Tinkerforge/gps-v2-bricklet/software/src/firefly_x1.c

/* gps-v2-bricklet
 * Copyright (C) 2016 Olaf Lüke <olaf@tinkerforge.com>
 * Copyright (C) 2020 Matthias Bolte <matthias@tinkerforge.com>
 *
 * firefly_x1.c: SPI communication with FireFly X1 GPS module
 *
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
 * You should have received a copy of the GNU Lesser General Public
 * License along with this library; if not, write to the
 * Free Software Foundation, Inc., 59 Temple Place - Suite 330,
 * Boston, MA 02111-1307, USA.
 */

#include "firefly_x1.h"

#include "xmc_spi.h"
#include "xmc_gpio.h"

#include "bricklib2/utility/ringbuffer.h"
#include "bricklib2/utility/led_flicker.h"
#include "bricklib2/protocols/tfp/tfp.h"
#include "bricklib2/hal/system_timer/system_timer.h"
#include "bricklib2/bootloader/bootloader.h"
#include "configs/config_firefly_x1.h"

#include "minmea.h"
#include "communication.h"

extern FireFlyX1 firefly_x1;

#define firefly_x1_rx_irq_handler IRQ_Hdlr_11
#define firefly_x1_tx_irq_handler IRQ_Hdlr_12

void __attribute__((optimize("-O3"))) firefly_x1_rx_irq_handler(void) {
	while(!XMC_USIC_CH_RXFIFO_IsEmpty(FIREFLY_X1_USIC)) {
		firefly_x1.ringbuffer_recv.buffer[firefly_x1.ringbuffer_recv.end] = FIREFLY_X1_USIC->OUTR;
		firefly_x1.ringbuffer_recv.end = (firefly_x1.ringbuffer_recv.end + 1) & FIREFLY_X1_RECV_BUFFER_MASK;

		firefly_x1.buffer_recv_counter++;
	}
}

void __attribute__((optimize("-O3"))) firefly_x1_tx_irq_handler(void) {
	while(!XMC_USIC_CH_TXFIFO_IsFull(FIREFLY_X1_USIC)) {
		FIREFLY_X1_USIC->IN[0] = firefly_x1.buffer_send[firefly_x1.buffer_send_index];
		firefly_x1.buffer_send_index++;
		if(firefly_x1.buffer_send_index == FIREFLY_X1_SEND_BUFFER_SIZE) {
			XMC_USIC_CH_TXFIFO_DisableEvent(FIREFLY_X1_USIC, XMC_USIC_CH_TXFIFO_EVENT_CONF_STANDARD);
			return;
		}
	}
}

void firefly_x1_init(FireFlyX1 *firefly_x1) {
	// Initialize the whole struct as zero
	memset(firefly_x1, 0, sizeof(FireFlyX1));
	firefly_x1->buffer_send_index = 0;
	firefly_x1->state = FIREFLY_X1_STATE_WAIT_FOR_INTERRUPT;
	firefly_x1->wait_8ms_start_time = 0;
	firefly_x1->fix_led_state.config = LED_FLICKER_CONFIG_EXTERNAL;
	firefly_x1->fix_led_config = GPS_V2_FIX_LED_CONFIG_SHOW_FIX;
	ringbuffer_init(&firefly_x1->ringbuffer_recv, FIREFLY_X1_RECV_BUFFER_SIZE, (uint8_t*)firefly_x1->buffer_recv);

	// USIC channel configuration
	const XMC_SPI_CH_CONFIG_t channel_config = {
		.baudrate       = 100000,
		.bus_mode       = XMC_SPI_CH_BUS_MODE_MASTER,
		.selo_inversion = XMC_SPI_CH_SLAVE_SEL_INV_TO_MSLS,
		.parity_mode    = XMC_USIC_CH_PARITY_MODE_NONE
	};

	// MISO pin configuration
	const XMC_GPIO_CONFIG_t mosi_pin_config = {
		.mode             = FIREFLY_X1_MOSI_PIN_AF,
		.output_level     = XMC_GPIO_OUTPUT_LEVEL_HIGH
	};

	// MOSI pin configuration
	const XMC_GPIO_CONFIG_t miso_pin_config = {
		.mode             = XMC_GPIO_MODE_INPUT_TRISTATE,
		.input_hysteresis = XMC_GPIO_INPUT_HYSTERESIS_STANDARD
	};

	// SCLK pin configuration
	const XMC_GPIO_CONFIG_t sclk_pin_config = {
		.mode             = FIREFLY_X1_SCLK_PIN_AF,
		.output_level     = XMC_GPIO_OUTPUT_LEVEL_HIGH
	};

	// SELECT pin configuration
	const XMC_GPIO_CONFIG_t select_pin_config = {
		.mode             = FIREFLY_X1_SELECT_PIN_AF,
		.output_level     = XMC_GPIO_OUTPUT_LEVEL_HIGH
	};

	// Interrupt pin configuration
	const XMC_GPIO_CONFIG_t interrupt_pin_config = {
		.mode             = XMC_GPIO_MODE_INPUT_TRISTATE,
		.output_level     = XMC_GPIO_OUTPUT_LEVEL_HIGH,
		.input_hysteresis = XMC_GPIO_INPUT_HYSTERESIS_STANDARD
	};

	// Reset pin configuration
	const XMC_GPIO_CONFIG_t nreset_pin_config = {
		.mode             = XMC_GPIO_MODE_OUTPUT_PUSH_PULL,
		.output_level     = XMC_GPIO_OUTPUT_LEVEL_HIGH, // not reset
	};

	// PPS pin configuration
	const XMC_GPIO_CONFIG_t pps_pin_config = {
		.mode             = XMC_GPIO_MODE_INPUT_TRISTATE,
		.output_level     = XMC_GPIO_OUTPUT_LEVEL_HIGH,
		.input_hysteresis = XMC_GPIO_INPUT_HYSTERESIS_STANDARD
	};

	// LED pin configuration
	XMC_GPIO_CONFIG_t led_pin_config = {
		.mode             = XMC_GPIO_MODE_OUTPUT_PUSH_PULL,
		.output_level     = XMC_GPIO_OUTPUT_LEVEL_LOW
	};

	// Configure GPIO pins
	XMC_GPIO_Init(FIREFLY_X1_INTERRUPT_PIN, &interrupt_pin_config);
	XMC_GPIO_Init(FIREFLY_X1_NRESET_PIN, &nreset_pin_config);
	XMC_GPIO_Init(FIREFLY_X1_PPS_PIN, &pps_pin_config);
	XMC_GPIO_Init(FIREFLY_X1_FIX_LED_PIN, &led_pin_config);

	// Configure MISO pin
	XMC_GPIO_Init(FIREFLY_X1_MOSI_PIN, &miso_pin_config);

	// Initialize USIC channel in SPI master mode
	XMC_SPI_CH_Init(FIREFLY_X1_USIC, &channel_config);
	FIREFLY_X1_USIC->SCTR &= ~USIC_CH_SCTR_PDL_Msk; // Set passive data level to 0

	XMC_SPI_CH_SetBitOrderMsbFirst(FIREFLY_X1_USIC);

	XMC_SPI_CH_SetWordLength(FIREFLY_X1_USIC, (uint8_t)8U);
	XMC_SPI_CH_SetFrameLength(FIREFLY_X1_USIC, (uint8_t)64U);

	XMC_SPI_CH_SetTransmitMode(FIREFLY_X1_USIC, XMC_SPI_CH_MODE_STANDARD);

	// Configure the clock polarity and clock delay
	XMC_SPI_CH_ConfigureShiftClockOutput(FIREFLY_X1_USIC,
									     XMC_SPI_CH_BRG_SHIFT_CLOCK_PASSIVE_LEVEL_1_DELAY_DISABLED,
									     XMC_SPI_CH_BRG_SHIFT_CLOCK_OUTPUT_SCLK);
	// Configure Leading/Trailing delay
	XMC_SPI_CH_SetSlaveSelectDelay(FIREFLY_X1_USIC, 2);

	// Set input source path
	XMC_SPI_CH_SetInputSource(FIREFLY_X1_USIC, FIREFLY_X1_MISO_INPUT, FIREFLY_X1_MISO_SOURCE);

	// SPI Mode: CPOL=1 and CPHA=1
	FIREFLY_X1_USIC_CHANNEL->DX1CR |= USIC_CH_DX1CR_DPOL_Msk;

	// Configure transmit FIFO
	XMC_USIC_CH_TXFIFO_Configure(FIREFLY_X1_USIC, 48, XMC_USIC_CH_FIFO_SIZE_16WORDS, 8);

	// Configure receive FIFO
	XMC_USIC_CH_RXFIFO_Configure(FIREFLY_X1_USIC, 32, XMC_USIC_CH_FIFO_SIZE_16WORDS, 0);
//	FIREFLY_X1_USIC->RBCTR |= USIC_CH_RBCTR_SRBTM_Msk; // RX Interrupt for >= 0

	// Set service request for tx FIFO transmit interrupt
	XMC_USIC_CH_TXFIFO_SetInterruptNodePointer(FIREFLY_X1_USIC, XMC_USIC_CH_TXFIFO_INTERRUPT_NODE_POINTER_STANDARD, FIREFLY_X1_SERVICE_REQUEST_TX);  // IRQ FIREFLY_X1_IRQ_TX

	// Set service request for rx FIFO receive interrupt
	XMC_USIC_CH_RXFIFO_SetInterruptNodePointer(FIREFLY_X1_USIC, XMC_USIC_CH_RXFIFO_INTERRUPT_NODE_POINTER_STANDARD, FIREFLY_X1_SERVICE_REQUEST_RX);  // IRQ FIREFLY_X1_IRQ_RX
	XMC_USIC_CH_RXFIFO_SetInterruptNodePointer(FIREFLY_X1_USIC, XMC_USIC_CH_RXFIFO_INTERRUPT_NODE_POINTER_ALTERNATE, FIREFLY_X1_SERVICE_REQUEST_RX); // IRQ FIREFLY_X1_IRQ_RX

	// Set priority and enable NVIC node for transmit interrupt
	NVIC_SetPriority((IRQn_Type)FIREFLY_X1_IRQ_TX, FIREFLY_X1_IRQ_TX_PRIORITY);
	NVIC_EnableIRQ((IRQn_Type)FIREFLY_X1_IRQ_TX);

	// Set priority and enable NVIC node for receive interrupt
	NVIC_SetPriority((IRQn_Type)FIREFLY_X1_IRQ_RX, FIREFLY_X1_IRQ_RX_PRIORITY);
	NVIC_EnableIRQ((IRQn_Type)FIREFLY_X1_IRQ_RX);

	// Start SPI
	XMC_SPI_CH_Start(FIREFLY_X1_USIC);

	// Configure SCLK pin
	XMC_GPIO_Init(FIREFLY_X1_SCLK_PIN, &sclk_pin_config);

	// Configure slave select pin
	XMC_GPIO_Init(FIREFLY_X1_SELECT_PIN, &select_pin_config);

	// Configure MOSI pin
	XMC_GPIO_Init(FIREFLY_X1_MOSI_PIN, &mosi_pin_config);

//	XMC_USIC_CH_EnableEvent(FIREFLY_X1_USIC, (uint32_t)((uint32_t)XMC_USIC_CH_EVENT_STANDARD_RECEIVE | (uint32_t)XMC_USIC_CH_EVENT_ALTERNATIVE_RECEIVE));
	XMC_USIC_CH_RXFIFO_EnableEvent(FIREFLY_X1_USIC, XMC_USIC_CH_RXFIFO_EVENT_CONF_STANDARD | XMC_USIC_CH_RXFIFO_EVENT_CONF_ALTERNATE);

	firefly_x1->last_data_time = system_timer_get_ms();
	firefly_x1->last_interrupt_time = system_timer_get_ms();
	firefly_x1->last_send_time = system_timer_get_ms();
	firefly_x1->interrupt_active_high = true;

	firefly_x1->sbas_enabled = true;
	firefly_x1_update_sbas(firefly_x1);
}

void firefly_x1_update_sbas(FireFlyX1 *firefly_x1) {
	if(firefly_x1->sbas_enabled) {
		firefly_x1->sbas = FIREFLY_X1_SBAS_ENABLE | FIREFLY_X1_SBAS_5HZ;
	} else {
		firefly_x1->sbas = FIREFLY_X1_SBAS_DISABLE | FIREFLY_X1_SBAS_10HZ;
	}

	// We don't use uart, but we still have to increase the baudrate to get
	// update rates of above 1Hz.
	firefly_x1->sbas |= FIREFLY_X1_SBAS_BAUDRATE;
}

void firefly_x1_handle_sentence(FireFlyX1 *firefly_x1, const char *sentence) {
	enum minmea_sentence_id id = minmea_sentence_id(sentence, false);

	char talker_id[3];
	minmea_talker_id(talker_id, sentence);
	FireFlyX1Talker talker;

	if(talker_id[0] == 'G' && talker_id[1] == 'P') {
		talker = TALKER_GPS;
	} else if(talker_id[0] == 'G' && talker_id[1] == 'L') {
		talker = TALKER_GLONASS;
	} else if(talker_id[0] == 'G' && talker_id[1] == 'N') {
		talker = TALKER_MIXED;
	} else {
		// Unknown talker
		return;
	}

	firefly_x1->last_data_time = system_timer_get_ms();

	switch(id) {
		case MINMEA_INVALID: {
			break;
		}

		case MINMEA_UNKNOWN: {
			break;
		}

		case MINMEA_SENTENCE_RMC: {
			struct minmea_sentence_rmc rmc;
			if(!minmea_parse_rmc(&rmc, sentence)) {
				return;
			}

			if(firefly_x1->mixed.time.hours        != rmc.time.hours ||
			   firefly_x1->mixed.time.minutes      != rmc.time.minutes ||
			   firefly_x1->mixed.time.seconds      != rmc.time.seconds ||
			   firefly_x1->mixed.time.microseconds != rmc.time.microseconds ||
			   firefly_x1->mixed.date.year         != rmc.date.year ||
			   firefly_x1->mixed.date.month        != rmc.date.month ||
			   firefly_x1->mixed.date.day          != rmc.date.day) {
				firefly_x1->new_date_time = true;
			}
			if(firefly_x1->mixed.latitude.value    != rmc.latitude.value ||
			   firefly_x1->mixed.longitude.value   != rmc.longitude.value) {
				firefly_x1->new_coordinates = true;
			}
			if(firefly_x1->mixed.speed.value       != rmc.speed.value ||
			   firefly_x1->mixed.course.value      != rmc.course.value) {
				firefly_x1->new_motion = true;
			}

			firefly_x1->mixed.time      = rmc.time;
			firefly_x1->mixed.valid     = rmc.valid;
			firefly_x1->mixed.latitude  = rmc.latitude;
			firefly_x1->mixed.longitude = rmc.longitude;
			firefly_x1->mixed.speed     = rmc.speed; // knots
			firefly_x1->mixed.course    = rmc.course;
			firefly_x1->mixed.date      = rmc.date;
			firefly_x1->mixed.variation = rmc.variation;

			break;
		}

		case MINMEA_SENTENCE_GGA: {
			struct minmea_sentence_gga gga;
			if(!minmea_parse_gga(&gga, sentence)) {
				return;
			}

			if(firefly_x1->mixed.time.hours         != gga.time.hours ||
			   firefly_x1->mixed.time.minutes       != gga.time.minutes ||
			   firefly_x1->mixed.time.seconds       != gga.time.seconds ||
			   firefly_x1->mixed.time.microseconds  != gga.time.microseconds) {
				firefly_x1->new_date_time = true;
			}
			if(firefly_x1->mixed.latitude.value     != gga.latitude.value ||
			   firefly_x1->mixed.longitude.value    != gga.longitude.value) {
				firefly_x1->new_coordinates = true;
			}
			if(firefly_x1->mixed.fix_quality        != gga.fix_quality ||
			   firefly_x1->mixed.satellites_tracked != gga.satellites_tracked) {
				firefly_x1->new_status = true;
			}
			if(firefly_x1->mixed.altitude.value     != gga.altitude.value ||
			   firefly_x1->mixed.height.value       != gga.height.value) {
				firefly_x1->new_altitude = true;
			}

			firefly_x1->mixed.time               = gga.time;
			firefly_x1->mixed.latitude           = gga.latitude;
			firefly_x1->mixed.longitude          = gga.longitude;
			firefly_x1->mixed.fix_quality        = gga.fix_quality;
			firefly_x1->mixed.satellites_tracked = gga.satellites_tracked;
			firefly_x1->mixed.hdop               = gga.hdop;
			firefly_x1->mixed.altitude           = gga.altitude;
			firefly_x1->mixed.altitude_units     = gga.altitude_units;
			firefly_x1->mixed.height             = gga.height;
			firefly_x1->mixed.height_units       = gga.height_units;
			firefly_x1->mixed.dgps_age           = gga.dgps_age;

			break;
		}

		case MINMEA_SENTENCE_GSA: {
			struct minmea_sentence_gsa gsa;
			if(!minmea_parse_gsa(&gsa, sentence)) {
				return;
			}

			FireFlyX1DataSingle *single;
			if(talker == TALKER_GPS) {
				single = &firefly_x1->gps;
			} else if(talker == TALKER_GLONASS) {
				single = &firefly_x1->glonass;
			} else {
				return;
			}

		    single->mode = gsa.mode;
		    single->fix_type = gsa.fix_type;
		    memcpy(single->sats, gsa.sats, 12);
		    single->pdop = gsa.pdop;
		    single->hdop = gsa.hdop;
		    single->vdop = gsa.vdop;

			break;
		}

		case MINMEA_SENTENCE_GLL: {
			// Not supported by Firefly X1
			break;
		}

		case MINMEA_SENTENCE_GST: {
			// Not supported Firefly X1
			break;
		}

		case MINMEA_SENTENCE_GSV: {
			struct minmea_sentence_gsv gsv;
			if(!minmea_parse_gsv(&gsv, sentence)) {
				return;
			}

			FireFlyX1DataSingle *single;
			if(talker == TALKER_GPS) {
				single = &firefly_x1->gps;
			} else if(talker == TALKER_GLONASS) {
				single = &firefly_x1->glonass;
			} else {
				return;
			}

			for(uint8_t i = 0; i < 4; i++) {
				uint8_t pnr = gsv.sats[i].nr;
				if(pnr == 96) { // pnr 96 seems to always produce garbage values, we ignore it
					continue;
				}

				if(talker == TALKER_GLONASS) {
					pnr -= 64; // GLONASS IDs go from 65 to 96
				}
				if(pnr < 1 || pnr > 32) { // pnr should always be between 1 and 32
					continue;
				}

				single->sat_info[pnr-1].nr        = gsv.sats[i].nr;
				single->sat_info[pnr-1].azimuth   = gsv.sats[i].azimuth;
				single->sat_info[pnr-1].elevation = gsv.sats[i].elevation;
				single->sat_info[pnr-1].snr       = gsv.sats[i].snr;
			}

			break;
		}

		case MINMEA_SENTENCE_VTG: {
			struct minmea_sentence_vtg vtg;
			if(!minmea_parse_vtg(&vtg, sentence)) {
				return;
			}

			firefly_x1->mixed.true_track_degrees     = vtg.true_track_degrees;
			firefly_x1->mixed.magnetic_track_degrees = vtg.magnetic_track_degrees;
			firefly_x1->mixed.speed_knots            = vtg.speed_knots;
			firefly_x1->mixed.speed_kph              = vtg.speed_kph;
			firefly_x1->mixed.faa_mode               = vtg.faa_mode;

			break;
		}
	}
}

void firefly_x1_handle_state_wait_for_interrupt(FireFlyX1 *firefly_x1) {
	const bool interrupt = XMC_GPIO_GetInput(FIREFLY_X1_INTERRUPT_PIN) == firefly_x1->interrupt_active_high;

	if(interrupt || system_timer_is_time_elapsed_ms(firefly_x1->last_interrupt_time, FIREFLY_X1_INTERRUPT_TIMEOUT)) {
		if(!interrupt) {
			// No interrupt during timeout duration. Are we using the wrong interrupt active level?
			// Interrupt can be active-low (FireFly X1, FW version < 5) or active high (XM1110, FW version >= 5)
			firefly_x1->interrupt_active_high = !firefly_x1->interrupt_active_high;
		}

		firefly_x1->last_interrupt_time = system_timer_get_ms();
		memset(firefly_x1->buffer_send, 0xAA, FIREFLY_X1_SEND_BUFFER_SIZE);

		if(firefly_x1->restart != 0) {
			memset(&firefly_x1->mixed, 0, sizeof(FireFlyX1DataMixed));
			memset(&firefly_x1->gps, 0, sizeof(FireFlyX1DataSingle));
			memset(&firefly_x1->glonass, 0, sizeof(FireFlyX1DataSingle));
		}

		if(system_timer_is_time_elapsed_ms(firefly_x1->last_send_time, FIREFLY_X1_TIME_BETWEEN_SENDS)) {
			if(firefly_x1->restart & FIREFLY_X1_RESTART_HOT) {
				strcpy(firefly_x1->buffer_send, "$PMTK101*32\r\n");
				firefly_x1->restart &= ~FIREFLY_X1_RESTART_HOT;
			} else if(firefly_x1->restart & FIREFLY_X1_RESTART_WARM) {
				strcpy(firefly_x1->buffer_send, "$PMTK102*31\r\n");
				firefly_x1->restart &= ~FIREFLY_X1_RESTART_WARM;
			} else if(firefly_x1->restart & FIREFLY_X1_RESTART_COLD) {
				strcpy(firefly_x1->buffer_send, "$PMTK103*30\r\n");
				firefly_x1->restart &= ~FIREFLY_X1_RESTART_COLD;
				firefly_x1_update_sbas(firefly_x1); // cold restart clears SBAS settings
			} else if(firefly_x1->restart & FIREFLY_X1_RESTART_FACTORY) {
				strcpy(firefly_x1->buffer_send, "$PMTK104*37\r\n");
				firefly_x1->restart &= ~FIREFLY_X1_RESTART_FACTORY;
				firefly_x1_update_sbas(firefly_x1); // factory-reset clears SBAS settings
			} else if(firefly_x1->sbas & FIREFLY_X1_SBAS_BAUDRATE) {
				strcpy(firefly_x1->buffer_send, "$PMTK251,115200*1F\r\n");
				firefly_x1->sbas &= ~FIREFLY_X1_SBAS_BAUDRATE;
			} else if(firefly_x1->sbas & FIREFLY_X1_SBAS_DISABLE) {
				strcpy(firefly_x1->buffer_send, "$PMTK313,0*2F\r\n");
				firefly_x1->sbas &= ~FIREFLY_X1_SBAS_DISABLE;
			} else if(firefly_x1->sbas & FIREFLY_X1_SBAS_10HZ) {
				strcpy(firefly_x1->buffer_send, "$PMTK220,100*2F\r\n");
				firefly_x1->sbas &= ~FIREFLY_X1_SBAS_10HZ;
			} else if(firefly_x1->sbas & FIREFLY_X1_SBAS_5HZ) {
				strcpy(firefly_x1->buffer_send, "$PMTK220,200*2C\r\n");
				firefly_x1->sbas &= ~FIREFLY_X1_SBAS_5HZ;
			} else if(firefly_x1->sbas & FIREFLY_X1_SBAS_ENABLE) {
				strcpy(firefly_x1->buffer_send, "$PMTK313,1*2E\r\n");
				firefly_x1->sbas &= ~FIREFLY_X1_SBAS_ENABLE;
			}

			if(firefly_x1->buffer_send[0] == '$') {
				firefly_x1->last_send_time = system_timer_get_ms();
			}
		}

		// Start transfer
		firefly_x1->buffer_recv_counter = 0;
		firefly_x1->buffer_send_index = 0;
		XMC_SPI_CH_EnableSlaveSelect(FIREFLY_X1_USIC, XMC_SPI_CH_SLAVE_SELECT_0);
		XMC_USIC_CH_TXFIFO_EnableEvent(FIREFLY_X1_USIC, XMC_USIC_CH_TXFIFO_EVENT_CONF_STANDARD);
		XMC_USIC_CH_TriggerServiceRequest(FIREFLY_X1_USIC, FIREFLY_X1_SERVICE_REQUEST_TX);

		firefly_x1->state = FIREFLY_X1_STATE_RECEIVE_IN_PROGRESS;
	}
}

void firefly_x1_handle_state_receive_in_progress(FireFlyX1 *firefly_x1) {
	if(firefly_x1->buffer_recv_counter >= FIREFLY_X1_SEND_BUFFER_SIZE) {
		XMC_SPI_CH_DisableSlaveSelect(FIREFLY_X1_USIC);

		firefly_x1->wait_8ms_start_time = system_timer_get_ms();
		firefly_x1->state = FIREFLY_X1_STATE_WAIT_8MS;
	}
}

void firefly_x1_handle_state_wait_8ms(FireFlyX1 *firefly_x1) {
	if(system_timer_is_time_elapsed_ms(firefly_x1->wait_8ms_start_time, 8)) {
		firefly_x1->state = FIREFLY_X1_STATE_WAIT_FOR_INTERRUPT;
	}
}

void firefly_x1_handle_state_reset(FireFlyX1 *firefly_x1) {
	if(firefly_x1->reset_time == 0) {
		firefly_x1->reset_time = system_timer_get_ms();
		firefly_x1->last_data_time = system_timer_get_ms();
		XMC_GPIO_SetOutputLow(FIREFLY_X1_NRESET_PIN);
	} else if(system_timer_is_time_elapsed_ms(firefly_x1->reset_time, FIREFLY_X1_RESET_TIMEOUT)) {
		XMC_GPIO_SetOutputHigh(FIREFLY_X1_NRESET_PIN);
		firefly_x1->reset_time = 0;
		firefly_x1->state = FIREFLY_X1_STATE_WAIT_FOR_INTERRUPT;
	}
}

void firefly_x1_handle_ringbuffer(FireFlyX1 *firefly_x1) {
	static char sentence[FIREFLY_X1_MAX_SENTENCE_LENGTH+1] = {0};
	static int16_t index = 0;

	while(index < FIREFLY_X1_MAX_SENTENCE_LENGTH) {
		// Turn RX interrupt off during ringbuffer_get
		NVIC_DisableIRQ((IRQn_Type)FIREFLY_X1_IRQ_RX);
		__DSB();
		__ISB();
		if(!ringbuffer_get(&firefly_x1->ringbuffer_recv, (uint8_t*)&sentence[index])) {
			NVIC_EnableIRQ((IRQn_Type)FIREFLY_X1_IRQ_RX);
			break;
		}
		NVIC_EnableIRQ((IRQn_Type)FIREFLY_X1_IRQ_RX);

		if(sentence[index] == '\n') {
			continue;
		}
		if(sentence[index] == '\r') {
			sentence[index] = '\0';

			firefly_x1_handle_sentence(firefly_x1, sentence);
			memset(sentence, 0 , index+1);

			index = 0;

			// We return after each sentence, so we can return to bootloader
			// between sentences
			break;
		}
		index++;
	}

	if(index == FIREFLY_X1_MAX_SENTENCE_LENGTH) {
		// Sentence was longer then FIREFLY_X1_MAX_SENTENCE_LENGTH byte, we don't support this
		memset(sentence, 0 , FIREFLY_X1_MAX_SENTENCE_LENGTH);
		index = 0;
	}
}

void firefly_x1_handle_fix_led(FireFlyX1 *firefly_x1) {
	static bool last_pps_high = false;
	static uint32_t last_pps_led_on = 0;

	// Handle standard configurations (on, off, heartbeat)
	led_flicker_tick(&firefly_x1->fix_led_state, system_timer_get_ms(), FIREFLY_X1_FIX_LED_PIN);

	// Handle fix configuration
	if(firefly_x1->fix_led_config == GPS_V2_FIX_LED_CONFIG_SHOW_FIX) {
		if(firefly_x1->mixed.fix_quality == 0) {
			XMC_GPIO_SetOutputHigh(FIREFLY_X1_FIX_LED_PIN);
		} else {
			XMC_GPIO_SetOutputLow(FIREFLY_X1_FIX_LED_PIN);
		}
	} else if(firefly_x1->fix_led_config == GPS_V2_FIX_LED_CONFIG_SHOW_PPS) {
		if(XMC_GPIO_GetInput(FIREFLY_X1_PPS_PIN)) {
			if(!last_pps_high) {
				XMC_GPIO_SetOutputLow(FIREFLY_X1_FIX_LED_PIN);
				last_pps_led_on = system_timer_get_ms();
				last_pps_high = true;
			}
		} else {
			last_pps_high = false;
		}

		if(system_timer_is_time_elapsed_ms(last_pps_led_on, FIREFLY_X1_PPS_BLINK_TIME)) {
			XMC_GPIO_SetOutputHigh(FIREFLY_X1_FIX_LED_PIN);
		}
	}
}

void firefly_x1_tick(FireFlyX1 *firefly_x1) {
	switch(firefly_x1->state) {
		case FIREFLY_X1_STATE_WAIT_FOR_INTERRUPT:   firefly_x1_handle_state_wait_for_interrupt(firefly_x1);  break;
		case FIREFLY_X1_STATE_RECEIVE_IN_PROGRESS:  firefly_x1_handle_state_receive_in_progress(firefly_x1); break;
		case FIREFLY_X1_STATE_WAIT_8MS:             firefly_x1_handle_state_wait_8ms(firefly_x1);            break;
		case FIREFLY_X1_STATE_RESET:                firefly_x1_handle_state_reset(firefly_x1);               break;
	}

	firefly_x1_handle_ringbuffer(firefly_x1);
	firefly_x1_handle_fix_led(firefly_x1);

	if(system_timer_is_time_elapsed_ms(firefly_x1->last_data_time, FIREFLY_X1_DATA_TIMEOUT)) {
		firefly_x1->state = FIREFLY_X1_STATE_RESET;
	}
}
